discipulus-ex/Prosthetic-Hand/docs/assets/images/Loading Animation.gif

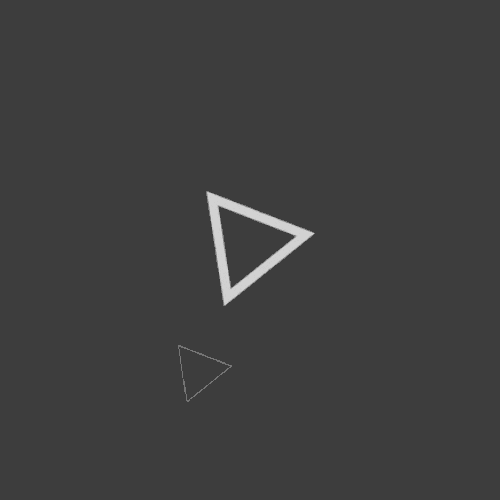
docs/assets/images/Loading Animation.gif
