discipulus-ex/Prosthetic-Hand/docs/dylan/ProstheticHand/images/IMG-20190212-WA0001.jpg

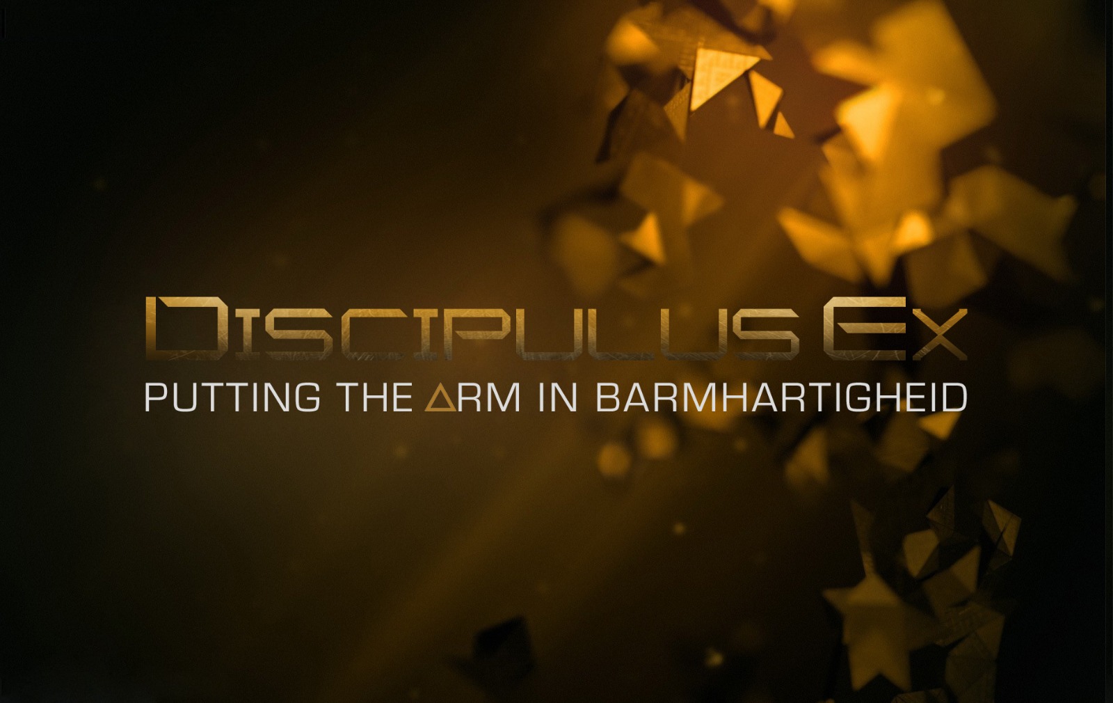
docs/dylan/ProstheticHand/images/IMG-20190212-WA0001.jpg
