discipulus-ex/Prosthetic-Hand/src/prostheticHand/main.h

/**
 * @file        main.cpp
 * @date        2019-06-19
 * @author      Dylan Duunk
 * 
 * @brief       Pin defines and callbacks
 */
#pragma once

#include "Arduino.h"
#include "Hand.h"

const int dataPin = A5;
const int latchPin = A6;
const int clockPin = A7;
