discipulus-ex/Prosthetic-Hand/docs/dylan/ProstheticHand/images/20190215_233537.jpg

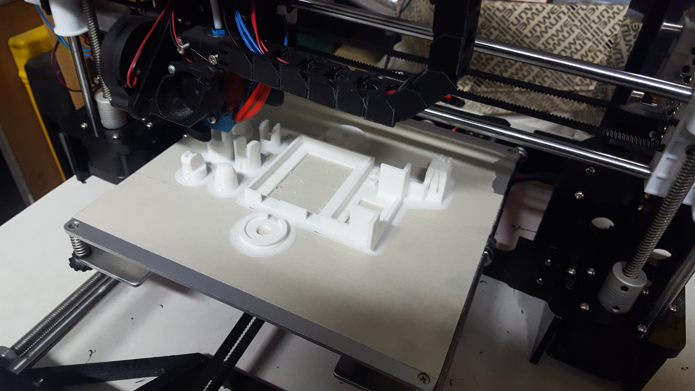
docs/dylan/ProstheticHand/images/20190215_233537.jpg
