discipulus-ex/Prosthetic-Hand/docs/dylan/ProstheticHand/images/20190219_122718.jpg

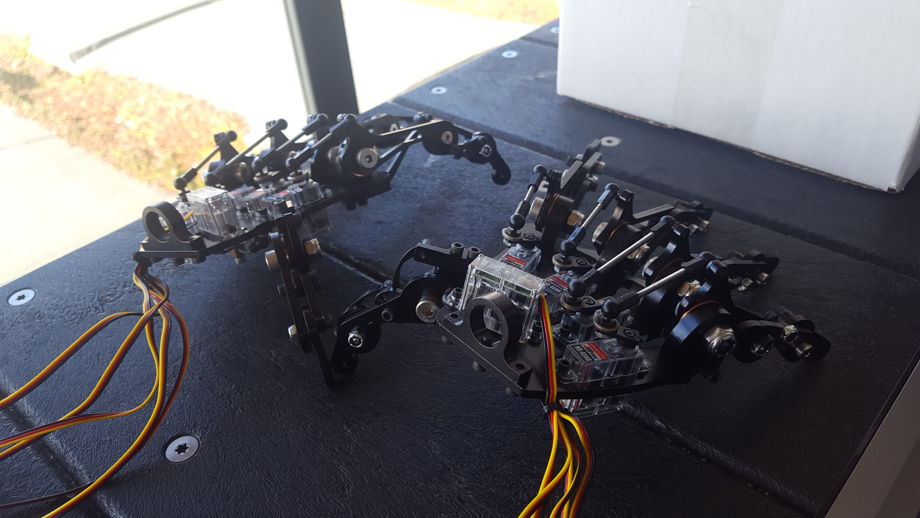
docs/dylan/ProstheticHand/images/20190219_122718.jpg
