discipulus-ex/Prosthetic-Hand/docs/dylan/ProstheticHand/images/20190219_122734.jpg

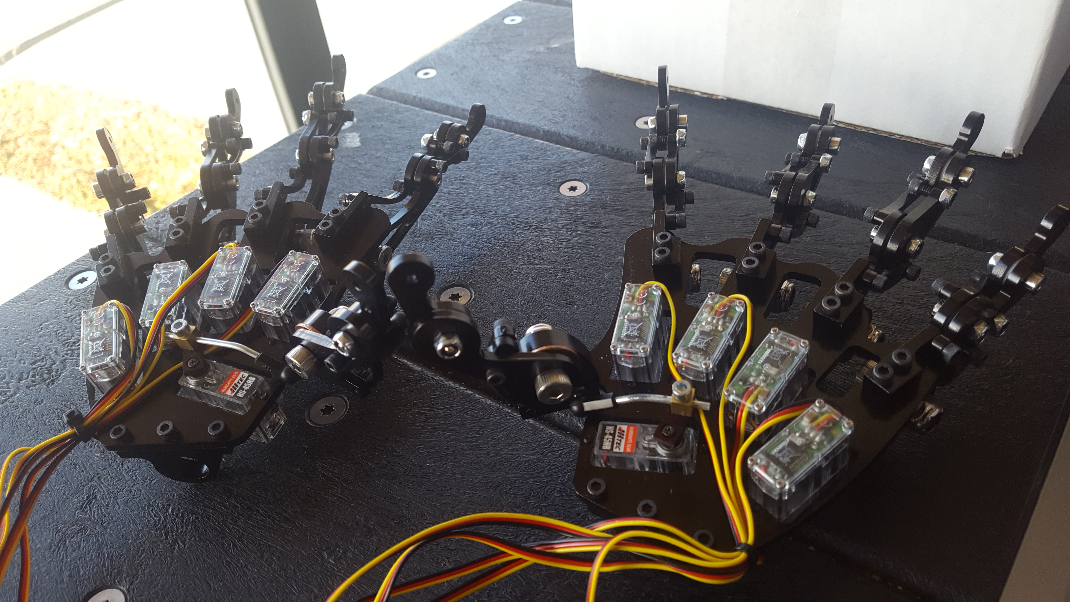
docs/dylan/ProstheticHand/images/20190219_122734.jpg
