discipulus-ex/Prosthetic-Hand/docs/dylan/ProstheticHand/images/20190219_122736.jpg

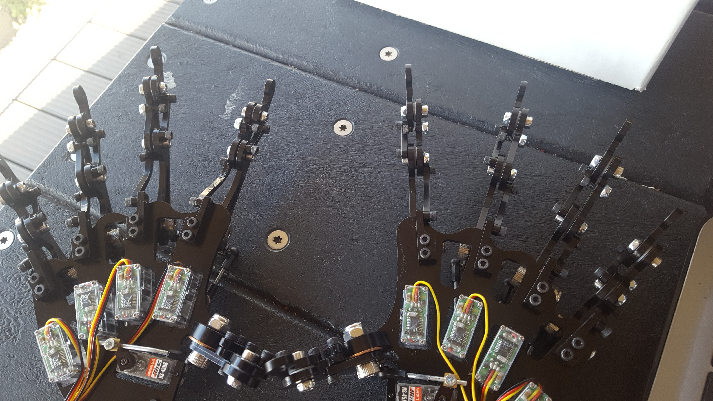
docs/dylan/ProstheticHand/images/20190219_122736.jpg
