discipulus-ex/Prosthetic-Hand/docs/dylan/ProstheticHand/images/20190303_115009.jpg

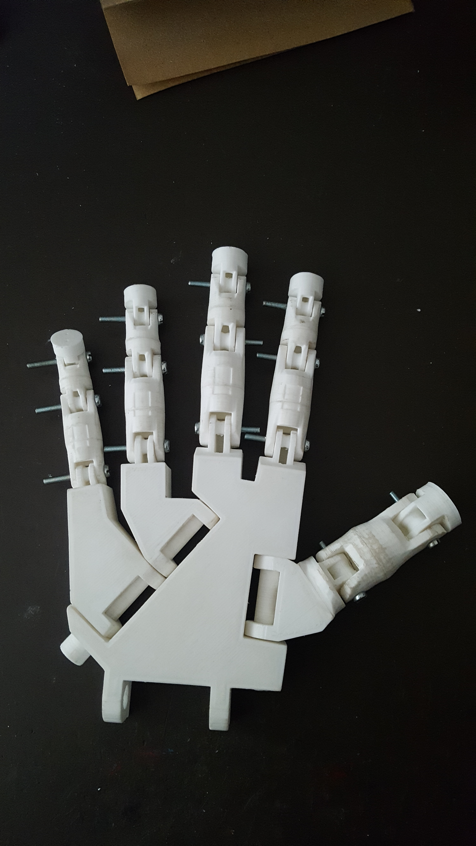
docs/dylan/ProstheticHand/images/20190303_115009.jpg
